wahart77399/RV-Bridge/src/Devices/Controllable/HVAC/FloorHeatView.cpp

#include "RVConstants.h"
#include "FloorHeatView.h"
#include "FloorHeat.h"
#include "Packet.h"
#include "DGN.h"
#include "debug.h"

float_t FloorHeatView::levelToTemperature(FLOOR_HEAT_LEVEL lvl) {
            return levelToTemperatureMap[lvl];
} 


boolean FloorHeatView::FloorHeatController::update(void) {
    boolean updated = false;
    if (/* (onOff != nullptr) && */ (targetTemp != nullptr) /* && (currentTemp != nullptr) */ && (model != nullptr) && (view != nullptr)) {
        view->dontUpdateTheView();
        if (/* onOff->updated()) { //  || */ targetTemp->updated() || targetState->updated()) {
            float_t closestTemp = view->closestTemperature(targetTemp->getNewVal<float_t>());
            //RV_PRINTF("FloorHeatView::FloorHeatController::update  - onOff: %d, targetTemp - %f\n", 
            //   onOff->getNewVal(), closestTemp);
            if (/* onOff->getNewVal() == false) { // || */ (targetState->getNewVal() == FLOOR_HEAT_OFF) || (closestTemp < FLOOR_HEAT_TEMP_STORE)) {
                model->turnFloorHeatOff();
                turnOff();
            } else {
                model->turnFloorHeatOn(closestTemp);
                turnOn();
                setTemperature(closestTemp);
            }
            updated = true;
        } 
        view->updateTheView();
    }
    return (updated);  
}


FloorHeatView::FloorHeatView(GenericDevice* model, const char* spanDevName) 
        : SpanView(model), controller(nullptr) {
}


bool FloorHeatView::updateView(void) {
    // RV_PRINTF("FloorHeatView::updateView called\n");
    bool updated = false;
    if (isNeedToUpdateView()) { // don't mess with the state of the lock when the change is is initiated by the controller and not the model
        uint8_t instance = indexOfModel();   
        uint8_t index = -1;
        FloorHeat* mdl = (FloorHeat* )getModel();
        if ((mdl != nullptr) && (controller != nullptr)) { 
            // RV_PRINTF("FloorHeatView::updateView - on = %d, & temp is %f\n", mdl->isTurnedOn(), mdl->currentFloorHeatSetting());
            if ((mdl->currentFloorHeatSetting() >= FLOOR_HEAT_TEMP_STORE) || mdl->isTurnedOn()) {
                //RV_PRINTF("FloorHeatView::updateView - on with temp = %f\n", mdl->currentFloorHeatSetting());
                controller->turnOn();
                controller->setTemperature(mdl->currentFloorHeatSetting() >= FLOOR_HEAT_TEMP_STORE ? 
                                            mdl->currentFloorHeatSetting() : FLOOR_HEAT_TEMP_STORE);

            } else {
                //RV_PRINTF("FloorHeatView::updateView - off\n");
                controller->turnOff();
            }
            updated = true;
        }        
    }

    // RV_PRINTF("FloorHeatView::updateView completed \n"); 
    return updated;
}

void FloorHeatView::createFloorHeatView(GenericDevice* model, const char* spanDevName) {
    RV_PRINTF("FloorHeatView::createAwningView called\n");

    FloorHeatView* vw = new FloorHeatView(model, spanDevName);

    SpanView::createAccessory();
    new Service::AccessoryInformation(); 
    new Characteristic::Identify();
    new Characteristic::Name(spanDevName);
    FloorHeatView::FloorHeatController* ctrl = new FloorHeatView::FloorHeatController(vw, (FloorHeat* )model);
    vw->setController(ctrl);

    if (vw != nullptr)
        RV_PRINTF("FloorHeatView::createAwningView: tmp created successfully\n");
    else
        RV_PRINTF("FloorHeatView::createAwningView: tmp creation failed\n");   
    RV_PRINTF("FloorHeatView::createAwningView completed\n");
}
