wahart77399/RV-Bridge/src/Devices/Controllable/HVAC/Thermostat.h

#ifndef THERMOSTAT_H
#define THERMOSTAT_H // once I'm ready to define this, move this below ifndef
/*********************************************************************************
 *  MIT License
 *  
 *  Copyright (c) 2023 Randy Ubillos
 *  
 *  https://github.com/rubillos/RV-Bridge
 *  
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
 ********************************************************************************/
 
////////////////////////////////////////////////////////////////
//                                                            //
//    RV-Bridge: A HomeKit to RV-C interface for the ESP32    //
//                                                            //
////////////////////////////////////////////////////////////////

//#define CUSTOM_CHAR_HEADER
#include "Arduino.h"
#include "GenericDevice.h"
#include "DGN.h"
#include "Packet.h"

#include "HVAC_defintions.h"
#include "RVConstants.h"
#include "debug.h"

// constexpr double  tempCOffset = -273.0;
// constexpr double  tempCScale = 0.03125;
// constexpr double  tempCRoundingOffset = -0.25;

class HVAC_Thermostat : public GenericDevice {

    private:
        // for THERMOSTAT_STATUS_1 which will be our base data
        const uint8_t THERMOSTAT_INDEX = 0;
        const uint8_t THERMOSTAT_OPERATING_MODE = 1;
        const uint8_t THERMOSTAT_FAN_SPEED = 2;
        const uint8_t THERMOSTAT_HEAT_TEMP_MSB = 3;
        const uint8_t THERMOSTAT_HEAT_TEMP_LSB = 4;
        const uint8_t THERMOSTAT_COOL_TEMP_MSB = 5;
        const uint8_t THERMOSTAT_COOL_TEMP_LSB = 6;
        const uint8_t OPERATING_MODE_MASK = 0x0f;
        const uint8_t FAN_MODE_MASK = 0x30;
        const uint8_t SCHEDULE_MODE_MASK = 0xc0;
        const uint8_t MAX_TEMP = 100;

        const uint8_t HEAT_TEMP_INDEX = 0;
        const uint8_t COLD_TEMP_INDEX = 1;
        uint16_t ambientTemperatureRaw_ = BAD_UINT16_DATA;
        bool ambientTemperatureAvailable_ = false;
        bool furnaceStatusAvailable_ = false;
        bool furnaceHeating_ = false;
        uint8_t airConditionerMode_ = 0xFF;
        uint8_t airConditionerMaxFanRaw_ = 0xFF;
        uint8_t heatPumpMode_ = 0xFF;
        uint8_t heatPumpMaxOutputRaw_ = 0xFF;
    public:
        /*
        static inline double convToTempC(uint16_t value) {
	        return tempCOffset + value * tempCScale + tempCRoundingOffset;  
        }
        static inline uint16_t convFromTempC(double tempC) {
	        return (tempC - tempCOffset + 0.5) / tempCScale;
        }
        */

    private:
        friend class ThermostatView;

        bool hasAmbientTemperature() const { return ambientTemperatureAvailable_; }
        double getAmbientTemperatureC() const {
            return ambientTemperatureAvailable_ ? convToTempC(ambientTemperatureRaw_) : INVALID_TEMPERATURE;
        }
        bool hasFurnaceStatus() const { return furnaceStatusAvailable_; }
        bool isFurnaceHeating() const { return furnaceHeating_; }
        void setAirConditionerStatus(const uint8_t* data) {
            if (data != nullptr) {
                airConditionerMode_ = data[1];
                airConditionerMaxFanRaw_ = data[2];
            }
        }
        void setHeatPumpStatus(const uint8_t* data) {
            if (data != nullptr) {
                heatPumpMode_ = data[1];
                heatPumpMaxOutputRaw_ = data[2];
            }
        }
        bool hasAirConditionerMode() const { return airConditionerMode_ <= 1; }
        uint8_t airConditionerMode() const { return airConditionerMode_; }
        bool hasAirConditionerMaxFan() const { return airConditionerMaxFanRaw_ <= MAX_RVC_PERCENT; }
        float airConditionerMaxFanPercent() const { return airConditionerMaxFanRaw_ * 0.5f; }
        bool hasHeatPumpMode() const { return heatPumpMode_ <= 1; }
        uint8_t heatPumpMode() const { return heatPumpMode_; }
        bool hasHeatPumpMaxOutput() const { return heatPumpMaxOutputRaw_ <= MAX_RVC_PERCENT; }
        float heatPumpMaxOutputPercent() const { return heatPumpMaxOutputRaw_ * 0.5f; }
        void setAmbientTemperature(const uint8_t* data) {
            if (data != nullptr) {
                ambientTemperatureRaw_ = static_cast<uint16_t>(data[1]) |
                                         (static_cast<uint16_t>(data[2]) << 8);
                double temperatureC = convToTempC(ambientTemperatureRaw_);
                ambientTemperatureAvailable_ = ambientTemperatureRaw_ != BAD_UINT16_DATA &&
                                               temperatureC >= -50.0 && temperatureC <= 100.0;
            }
        }
        void setFurnaceStatus(const uint8_t* data) {
            if (data != nullptr) {
                furnaceStatusAvailable_ = data[3] <= RVCPercentMax;
                furnaceHeating_ = furnaceStatusAvailable_ && data[3] > 0;
            }
        }

        void setFanMode(const RVCFanMode setting) {
            uint8_t* rawData = getCurrentData();
            if (rawData != nullptr) {
                uint8_t mode = rawData[THERMOSTAT_OPERATING_MODE];
                uint8_t mask = SCHEDULE_MODE_MASK | OPERATING_MODE_MASK;
                rawData[THERMOSTAT_OPERATING_MODE] = (mode & mask) | setting;
            }
        }
        void setOperatingMode(const RVCMode md) {
            uint8_t* rawData = getCurrentData();
            if (rawData != nullptr) {
                uint8_t mode = rawData[THERMOSTAT_OPERATING_MODE];
                uint8_t mask = SCHEDULE_MODE_MASK | FAN_MODE_MASK;
                rawData[THERMOSTAT_OPERATING_MODE] = (mode & mask) | md;
            }
        }

        void setFanSpeed(const RVCForcedFan speed) {
            uint8_t* rawData = getCurrentData();
            if (rawData != nullptr) {
                rawData[THERMOSTAT_FAN_SPEED] = speed;
            }
        }

        void setCoolTemp(const uint16_t tempC) {
            uint8_t* tempData = getCurrentData();
            if (tempData != nullptr) {
                uint16_t temp = convFromTempC(tempC);
                tempData[THERMOSTAT_COOL_TEMP_LSB] = temp >> 8;
                tempData[THERMOSTAT_COOL_TEMP_MSB] = temp & 0xff;
                RV_PRINTF("HVAC_Thermostat::setCoolTemp end - temp = tempData[5] %d, tempData[6] %d, Temp = %d", tempData[5], tempData[6], tempC);
            }
        }

        // all temps coming from °C to °C (storing in °C)
        void setHeatTemp(const uint16_t tempC) {
            uint8_t* tempData = getCurrentData();
            if (tempData != nullptr) {
                uint16_t temp = convFromTempC(tempC);
                tempData[THERMOSTAT_HEAT_TEMP_LSB] = temp >> 8;
                tempData[THERMOSTAT_HEAT_TEMP_MSB] = temp & 0xff;
            }
        }

        const RVCFanMode getFanMode(void) const {
            RVCFanMode modeResult = AUTO_FAN_MODE;
            uint8_t* rawData = getCurrentData();
            if (rawData != nullptr) {
                modeResult = (RVCFanMode) (rawData[THERMOSTAT_OPERATING_MODE] & FAN_MODE_MASK);
            }
            return modeResult;
        }

        const RVCForcedFan getFanSpeed(void) const {
            RVCForcedFan speed = AUTO_FAN;
            uint8_t* rawData = getCurrentData();
            if (rawData != nullptr) {
                speed = (RVCForcedFan) (rawData[THERMOSTAT_FAN_SPEED]);
            }
            return speed;
        }

        const RVCMode getOperatingMode(void) const {
            RVCMode modeResult = AUTO;
            uint8_t* rawData = getCurrentData();
            if (rawData != nullptr) {
                modeResult = (RVCMode) (rawData[THERMOSTAT_OPERATING_MODE] & OPERATING_MODE_MASK);
            }
            return modeResult;
        }

        const uint16_t getCoolTemp(void) const {
            uint16_t temp = DEFAULT_TEMP;
            uint8_t* tempData = getCurrentData();
            if (tempData != nullptr) {
                uint16_t tmp = convToTempC(tempData[THERMOSTAT_COOL_TEMP_LSB]<<8 | tempData[THERMOSTAT_COOL_TEMP_MSB]); 
                temp = (tmp < MAX_TEMP) ? tmp : DEFAULT_TEMP; //convFromTempC((double) tempC);

            }
            return temp;
        }

        const uint16_t getHeatTemp(void) const {
            uint16_t temp = DEFAULT_TEMP;
            uint8_t* tempData = getCurrentData();
            if (tempData != nullptr) {
                uint16_t tmp = convToTempC(tempData[THERMOSTAT_HEAT_TEMP_LSB]<<8 | tempData[THERMOSTAT_HEAT_TEMP_MSB]); 
                temp = (tmp < MAX_TEMP) ? tmp : DEFAULT_TEMP; //convFromTempC((double) tempC);
            }
            return temp;
        }

        boolean isFanAuto(void) const { return getFanMode() == AUTO_FAN_MODE; }

    protected:
        inline uint8_t* getCurrentData(void) const {
            return GenericDevice::getCurrentData();
        }
        
        virtual void setData(RVC_DGN dgn, uint8_t* data) {
            if (data != nullptr) {
                uint8_t* rawData = getCurrentData();
                uint8_t i = 1;
                if (rawData != nullptr) {// set the current data to the new data
                    switch (dgn) {
                        // COMMAND_1 and STATUS_1 have the same data format
                        case (THERMOSTAT_COMMAND_1):
                        case (THERMOSTAT_STATUS_1):
                            for (i = 1; i < 8; i++) // 8 bytes in a data payload
                                if (((i == 3) || (i == 4) || (i == 5) || (i==6)) && (data[i] == 0xff)) { // deals with out of bounds data
                                    rawData[i] = 0x24;
                                } else {
                                    rawData[i] = data[i];
                                }
                            break;
                    
                        default:
                            RV_PRINTF("********** WARNING: THESE THERMOSTAT DGNs ARE NOT SUPPORTED************* \n");
                            break;
                    }
                }
            }
        }

        virtual CAN_frame_t* buildCommand(RVC_DGN dgn);

    public:
        HVAC_Thermostat() : GenericDevice() { 
            // Constructor implementation
            
        }

        HVAC_Thermostat(const HVAC_Thermostat&) = delete;
        HVAC_Thermostat& operator=(const HVAC_Thermostat&) = delete;
        HVAC_Thermostat(HVAC_Thermostat&&) = delete;
        HVAC_Thermostat& operator=(HVAC_Thermostat&&) = delete;

        HVAC_Thermostat(uint8_t address, uint8_t instance) : GenericDevice(address, instance) {     
            
        }

        HVAC_Thermostat(uint8_t* data) : GenericDevice(data) {
            // Constructor with parameters implementation
        }

        virtual ~HVAC_Thermostat() {
            // Destructor implementation
        } 

        virtual boolean executeCommand(RVC_DGN dgn, const uint8_t* buffer, uint8_t val=SOURCE_ADDRESS);
};

#endif
