wahart77399/RV-Bridge/src/Devices/Controllable/HVAC/ThermostatView.cpp

/*********************************************************************************
 *  MIT License
 *  
 *  Copyright (c) 2023 Randy Ubillos
 *  
 *  https://github.com/rubillos/RV-Bridge
 *  
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
 ********************************************************************************/
 
////////////////////////////////////////////////////////////////
//                                                            //
//    RV-Bridge: A HomeKit to RV-C interface for the ESP32    //
//                                                            //
////////////////////////////////////////////////////////////////
#include "RVConstants.h"

#include "ThermostatView.h"
#include "Thermostat.h"
#include "Packet.h"
#include "DGN.h"
#include "debug.h"
 
bool ThermostatView::categoryCreated = false;
void ThermostatView::createCategory(void) {
    if (!categoryCreated) {
         categoryCreated = true;
    }
}
boolean ThermostatView::FanController::update(void) {
	bool updated = false;
    if ((_active != nullptr) && (speed != nullptr) && (targetState != nullptr) && (model != nullptr) && (view != nullptr)) {
        view->dontUpdateTheView();
	    if (_active->updated() || speed->updated() || targetState->updated()) {
		    RV_PRINTF("ThermostatView::FanController::update  - active: %d, speed - %d, targetState - %d\n", 
            _active->getNewVal(), speed->getNewVal(), targetState->getNewVal());
            // updated = view->updateView();
            if (speed->updated()) {
                float spd = speed->getNewVal();
                float lowSpeed = view->HomeKitPercentMax/2;
                RVCForcedFan newSpeed = AUTO_FAN;
                if (spd > 0)
                    newSpeed = (spd <= lowSpeed) ? LOW_FAN : HIGH_FAN;
                model->setFanSpeed(newSpeed);
            }
            if (_active->updated() && (_active->getNewVal() > 0)) 
                model->setFanMode(ON_FAN_MODE);
            else  
                model->setFanMode(AUTO_FAN_MODE);
            model->executeCommand(THERMOSTAT_COMMAND_1, model->getCurrentData());
        }
        view->updateTheView();
    }
	return (updated);  
}

RVCFanMode ThermostatView::FanController::getMode(void) const {
    RVCFanMode mode = AUTO_FAN_MODE;
    if ((_active != nullptr) && (_active->getVal() > 0))
        mode = ON_FAN_MODE;
    return mode;
}

uint16_t ThermostatView::FanController::getSpeed(void) const {
    uint16_t speedResult = (uint16_t) AUTO_FAN;
    if (speed != nullptr) {
        float spd = speed->getVal();
        float lowSpeed = view->HomeKitPercentMax/2;
        if (spd > 0)
            speedResult = (spd <= lowSpeed) ? (uint16_t) LOW_FAN : (uint16_t) HIGH_FAN;
    }
    return speedResult;
}

#include "PacketQueue.h"

 void ThermostatView::FanController::setModeSpeed(uint8_t fanMode, uint8_t spd) {
	bool newActive = fanMode == ON_FAN_MODE;

    if (view != nullptr) {
    	spd = spd * view->HomeKitPercentMax / RVCPercentMax;

	    if ((_active != nullptr) && (newActive != _active->getVal())) {
		    RV_PRINTF("Thermostat::FanController::setModeSpeed #%d - setActive: %d\n", (uint32_t)millis(), model->index(), newActive);
		    _active->setVal(newActive);
	    }
	    if ((speed != nullptr) && (spd != speed->getVal())) {
		    RV_PRINTF("Thermostat::FanController::setModeSpeed #%d - setSpeed: %d\n", model->index(), spd);
		    speed->setVal((spd < 100) ? spd : INITIAL_ROTATION_SPEED);
        }
        PacketQueue::clearLastPacketReceiveTime();
    }
} 



void ThermostatView::FanController::setLevel(uint8_t level) {
	bool on = level > 0;
	bool changed = false;

    if ((model != nullptr) && (!model->isFanAuto())) {
        if ((level > 0) && (level <= view->HomeKitPercentMax)) {
            currentState->setVal(currentFanStateBlowing);
        } else {
            currentState->setVal(currentFanStateIdle);
        }
        PacketQueue::clearLastPacketReceiveTime();
    }
} 
    //*/


typedef enum {
    THERM_OFF=0,
    THERM_HEAT = 1,
    THERM_COOL = 2,
    THERM_AUTO = 3
} HomeKitOperatingMode;

boolean ThermostatView::ThermostatController::update(void) {
    boolean updated = false;
    if ((targetState != nullptr) && (targetTemp != nullptr) && (model != nullptr) && (view != nullptr)) {
        view->dontUpdateTheView();
        HVAC_Thermostat* myModel = model;
        if (targetState->updated()) {
            switch(targetState->getNewVal()) {
                case (THERM_OFF):
                    myModel->setOperatingMode(RVCMode::OFF);
                    break;
                case (THERM_HEAT):
                    myModel->setOperatingMode(RVCMode::HEAT);
                    break;
                case(THERM_COOL):
                    myModel->setOperatingMode(RVCMode::COOL);
                    break;
                case(THERM_AUTO):
                default:
                    myModel->setOperatingMode(RVCMode::AUTO);
                    break;
            }
            updated = true;
        }
        if (targetTemp->updated()) {
            RVCMode md = myModel->getOperatingMode();
            float temp = targetTemp->getNewVal();
            switch (md) {
                case (RVCMode::COOL):
                    myModel->setCoolTemp(temp);
                    break;
                case(RVCMode::HEAT):
                    myModel->setHeatTemp(temp);
                    break;
                case (RVCMode::AUTO):
                    myModel->setCoolTemp(temp);
                    myModel->setHeatTemp((temp - 4.0));
                    break;
                case(RVCMode::OFF):
                default:
                    // do nothing
                    break;
            }
        }
        myModel->executeCommand(THERMOSTAT_COMMAND_1, myModel->getCurrentData());
        updated = true;
        view->updateTheView();
    }
    return updated;
}

void ThermostatView::ThermostatController::setInfo(RVCMode opMode, RVCFanMode fanMode, RVCForcedFan fanSpeed,
                                                   double heatTemp, double coolTemp, bool hasAmbientTemp,
                                                   double ambientTempC, bool hasFurnaceStatus,
                                                   bool furnaceHeating) {
    if ((currentState != nullptr) && (targetState != nullptr) && (targetTemp != nullptr) && (fan != nullptr) && (ambientTemp != nullptr)) {
        if (hasAmbientTemp && fabs(ambientTemp->getVal<double>() - ambientTempC) > 0.05) {
            ambientTemp->setVal(ambientTempC);
        }
        HomeKitOperatingMode homeKitOperatingMode = static_cast<HomeKitOperatingMode>(targetState->getVal<uint8_t>());
        switch(opMode) {
            case (RVCMode::COOL):
                
                switch (homeKitOperatingMode) {
                    case(THERM_OFF):
                    case(THERM_AUTO):
                    case(THERM_HEAT):
                        targetState->setVal(THERM_COOL);
                        break;
                    case(THERM_COOL):
                    default:
                        break;
                        // do nothing
                }
                if (fabs(coolTemp - targetTemp->getVal<double>()) > 0.2) {
	    			    // RV_PRINTF("ThermostatView::ThermostatController - Cool Thermostat #%d: targetTemp = %f\n", model->index(), coolTemp);
		    		    targetTemp->setVal(coolTemp);
		        }
                
                break;
            case (RVCMode::HEAT):
                switch(homeKitOperatingMode) {
                    case(THERM_OFF):
                    case(THERM_AUTO):
                    case(THERM_COOL):
                        targetState->setVal(THERM_HEAT);
                        break;
                    case(THERM_HEAT):
                    default:
                        break;
                        // do nothing
                }
                if (fabs(heatTemp - targetTemp->getVal<double>()) > 0.2) {
	    			    // RV_PRINTF("ThermostatView::ThermostatController - Heat Thermostat #%d: targetTemp = %f\n", model->index(), heatTemp);
		    		    targetTemp->setVal(heatTemp);
		        }
                break;
            case (RVCMode::AUTO):
                switch(homeKitOperatingMode) {
                    case(THERM_OFF):
                    case(THERM_COOL):
                    case(THERM_HEAT):
                        targetState->setVal(THERM_AUTO);
                        break;
                    case (THERM_AUTO):
                    default:
                        // do nothing
                        break;
                }
                if (ambientTemp->getVal() > coolTemp) 
                    targetTemp->setVal(coolTemp);
                else if (ambientTemp->getVal() < heatTemp)
                    targetTemp->setVal(heatTemp);
                break;
            case (RVCMode::OFF):
                switch(homeKitOperatingMode) {
                    case(THERM_COOL):
                    case(THERM_HEAT):
                    case(THERM_AUTO):
                        targetState->setVal(THERM_OFF);
                        break;
                    case(THERM_OFF):
                    default:
                        // do nothing
                        break;
                }
                break;
            default:
                break;
        }
        if (hasFurnaceStatus) {
            uint8_t heatingState = furnaceHeating
                ? HomeKitHVACStates::heatingCoolingStateHeat
                : HomeKitHVACStates::heatingCoolingStateOff;
            if (currentState->getVal<uint8_t>() != heatingState) currentState->setVal(heatingState);
        }
        fan->setModeSpeed(fanMode, fanSpeed);
        PacketQueue::clearLastPacketReceiveTime();
    }
}

#include "ChassisMobility.h"

bool ThermostatView::updateView(void) {
        // 
    // RV_PRINTF("DoorLockView::updateView called\n");
    bool updated = false;
    if (isNeedToUpdateView() && ChassisMobility::isParked()) { // don't mess with the state of the lock when the change is is initiated by the controller and not the model
        uint8_t instance = indexOfModel();   
        uint8_t index = -1;
        HVAC_Thermostat* mdl = (HVAC_Thermostat* )getModel();
        if ((mdl != nullptr) && (controller != nullptr)) {
            RVCFanMode fanMode = mdl->getFanMode();
            RVCMode opMode = mdl->getOperatingMode();
            RVCForcedFan fanSpeed = mdl->getFanSpeed();
            float coolTemp = mdl->getCoolTemp();
            float heatTemp = mdl->getHeatTemp();
            controller->setInfo(opMode, fanMode, fanSpeed, heatTemp, coolTemp,
                                mdl->hasAmbientTemperature(), mdl->getAmbientTemperatureC(),
                                mdl->hasFurnaceStatus(), mdl->isFurnaceHeating());
            if (mdl->hasAirConditionerMode() && airConditionerModeChar_ != nullptr) {
                airConditionerModeChar_->setVal(tempCfromTempF(mdl->airConditionerMode()));
            }
            if (mdl->hasAirConditionerMaxFan() && airConditionerMaxFanChar_ != nullptr) {
                airConditionerMaxFanChar_->setVal(tempCfromTempF(mdl->airConditionerMaxFanPercent()));
            }
            if (mdl->hasHeatPumpMode() && heatPumpModeChar_ != nullptr) {
                heatPumpModeChar_->setVal(tempCfromTempF(mdl->heatPumpMode()));
            }
            if (mdl->hasHeatPumpMaxOutput() && heatPumpMaxOutputChar_ != nullptr) {
                heatPumpMaxOutputChar_->setVal(tempCfromTempF(mdl->heatPumpMaxOutputPercent()));
            }
            updated = true; 
        }
    }
    // RV_PRINTF("DoorLockView::updateView completed \n"); 
    return updated;
 }

 ThermostatView::ThermostatView(GenericDevice* model, const char* spanDevName)
     : SpanView(model)
     , controller(nullptr)
     , airConditionerModeChar_(nullptr)
     , airConditionerMaxFanChar_(nullptr)
     , heatPumpModeChar_(nullptr)
     , heatPumpMaxOutputChar_(nullptr) {

 }

 void ThermostatView::createThermostatView(GenericDevice* model, const char* spanDevName) {
    RV_PRINTF("ThermostatView::createThermostatView called\n");
    SpanView::prepHomeSpan();

    ThermostatView* vw = new ThermostatView(model, spanDevName);

    ThermostatView::createCategory();

    const String fanName = String(spanDevName) + " Fan";
    SpanView::createAccessory();
    new Service::AccessoryInformation(); 
    new Characteristic::Identify();
    new Characteristic::Name(fanName.c_str());
    ThermostatView::FanController* fn = new ThermostatView::FanController(vw, (HVAC_Thermostat*)model);

    SpanView::createAccessory();
    new Service::AccessoryInformation(); 
    new Characteristic::Identify();
    new Characteristic::Name(spanDevName);

    ThermostatView::ThermostatController* controller = new ThermostatView::ThermostatController(vw, model, fn, spanDevName);
    vw->setController(controller);

    new Service::TemperatureSensor();
        new Characteristic::ConfiguredName("A/C Mode (0 Auto, 1 Manual)");
    vw->airConditionerModeChar_ = new Characteristic::CurrentTemperature(tempCfromTempF(0));
    vw->airConditionerModeChar_->setRange(tempCfromTempF(0), tempCfromTempF(1));

    new Service::TemperatureSensor();
        new Characteristic::ConfiguredName("A/C Max Fan Speed (%)");
    vw->airConditionerMaxFanChar_ = new Characteristic::CurrentTemperature(tempCfromTempF(0));
    vw->airConditionerMaxFanChar_->setRange(tempCfromTempF(0), tempCfromTempF(MAX_RVC_PERCENT * RVC_PERCENT_PRECISION));

    new Service::TemperatureSensor();
        new Characteristic::ConfiguredName("Heat Pump Mode (0 Auto, 1 Manual)");
    vw->heatPumpModeChar_ = new Characteristic::CurrentTemperature(tempCfromTempF(0));
    vw->heatPumpModeChar_->setRange(tempCfromTempF(0), tempCfromTempF(1));

    new Service::TemperatureSensor();
        new Characteristic::ConfiguredName("Heat Pump Max Output (%)");
    vw->heatPumpMaxOutputChar_ = new Characteristic::CurrentTemperature(tempCfromTempF(0));
    vw->heatPumpMaxOutputChar_->setRange(tempCfromTempF(0), tempCfromTempF(MAX_RVC_PERCENT * RVC_PERCENT_PRECISION));


    if (vw != nullptr)
        RV_PRINTF("ThermostatView::createThermostatView: tmp created successfully\n");
    else
        RV_PRINTF("ThermostatView::createThermostatView: tmp creation failed\n");   
    RV_PRINTF("ThermostatView::createThermostatView completed\n");
}
