wahart77399/RV-Bridge/src/Devices/Sensors/Power/Battery.h

#include "RVConstants.h"
#include "debug.h"
#ifndef BATTERY_H
#define BATTERY_H // once I'm ready to define this, move this below ifndef

/*********************************************************************************
 *  MIT License
 *  
 *  Copyright (c) 2023 Randy Ubillos
 *  
 *  https://github.com/rubillos/RV-Bridge
 *  
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
 ********************************************************************************/
 
////////////////////////////////////////////////////////////////
//                                                            //
//    RV-Bridge: A HomeKit to RV-C interface for the ESP32    //
//                                                            //
////////////////////////////////////////////////////////////////

//#define CUSTOM_CHAR_HEADER
#include "Arduino.h"
#include "GenericDevice.h"
#include "RVConstants.h"
#include "BatteryDefinitions.h"
#include "byteswap.h"
#include <limits>

class Battery : public GenericDevice {
    private:
         
        uint8_t* source2Data;
        uint8_t* source3Data;
        uint8_t* source4Data;
        bool dcDisconnectStatusAvailable_ = false;
        bool dcConnected_ = false;

        const uint8_t TIME_TO_EMPTY = 0x00;
        const uint8_t TIME_TO_FULL = 0x01;
        friend class BatteryView;
        uint8_t* getSource1Data(void) const { return getCurrentData();} 
        uint8_t* getSource2Data(void) const { return source2Data; }
        uint8_t* getSource3Data(void) const { return source3Data; }
        uint8_t* getSource4Data(void) const { return source4Data; }

        static inline uint32_t rd_le32(const uint8_t* p) {
            return (uint32_t)p[0] | ((uint32_t)p[1] << 8) | ((uint32_t)p[2] << 16) | ((uint32_t)p[3] << 24);
        }

        void setDataFromSource(uint8_t* source, uint8_t* destination) {
            if ((source != nullptr) && (destination != nullptr)) {
                for (int i = DC_SOURCE_PRIORITY_INDEX; i < (DC_SOURCE_CURRENT_LSB_2_INDEX + 1); i++)
                    destination[i] = source[i];
            }
        }

        const DC_SOURCE_INSTANCE_DEFINITION getSourceDefinition(void) const {
            DC_SOURCE_INSTANCE_DEFINITION result = INVALID_SOURCE;
            uint8_t* data = getCurrentData();
            if (data != nullptr)
                result = (DC_SOURCE_INSTANCE_DEFINITION) data[DC_SOURCE_INSTANCE_INDEX];
            return result;
        }

        const DC_SOURCE_PRIORITY_DEFINTION getPirorityDefinition(void) const {
            DC_SOURCE_PRIORITY_DEFINTION result = NO_PRIORITY_ALWAYS_RPT;
            uint8_t* data = getCurrentData();
            if (data != nullptr)
                result = (DC_SOURCE_PRIORITY_DEFINTION) data[DC_SOURCE_PRIORITY_INDEX];
            return result;
        }

        // SOURCE 1 STATUS Data
        float_t directCurrentVoltage(void) const {
            uint8_t* data = getSource1Data();
            uint16_t value = 0;
            float_t result = std::numeric_limits<float_t>::quiet_NaN();
            if (data != nullptr) {
                value = getLilEndian(data[DC_SOURCE_VOLTAGE_MSB_INDEX], data[DC_SOURCE_VOLTAGE_LSB_INDEX]);
                if (value <= VDC_RAW_MAX)
                    result = (value - VDC_OFFSET) * VDC_PRECISION;
            }
            return result;
        }

        float directCurrentAmperage(void) const {
            uint8_t* data = getSource1Data();
            float result = std::numeric_limits<float>::quiet_NaN();
            if (data != nullptr) {
                const uint8_t* cur = &data[DC_SOURCE_CURRENT_MSB_1_INDEX];
                uint32_t raw = rd_le32(cur);
                if (raw != 0xFFFFFFFFu) {
                    result = (static_cast<float>(static_cast<int64_t>(raw) - static_cast<int64_t>(ADC_ZERO))) 
                              * static_cast<float>(ADC_PRECISION);
                }
            }
            return result;
        }

        // SOURCE 2 STATUS DATA
        const double temperature(void) const {
            uint8_t* data = getSource2Data();
            double result = INVALID_TEMPERATURE;
            if (data != nullptr) {
                uint16_t rawTemperature = getLilEndian(data[DC_SOURCE_TEMPERATURE_MSB_INDEX], data[DC_SOURCE_TEMPERATURE_LSB_INDEX]);
                if (rawTemperature != BAD_UINT16_DATA) {
                    result = convToTempC(rawTemperature);
                }
                // RV_PRINTF("Battery::temperature = %d\n", result);
            }
            return result;
        }

        uint8_t level(void) const {
            uint8_t* data = getSource2Data();
            uint8_t result = OUT_OF_RANGE_DATA;
            if ((data != nullptr) && (data[DC_SOURCE_STATE_OF_CHARGE_INDEX] <= MAX_RVC_PERCENT)) {
                uint8_t tmp = data[DC_SOURCE_STATE_OF_CHARGE_INDEX];
                RV_PRINTF("Battery::level tmp = %d\n", tmp);
                result = static_cast<uint8_t>(static_cast<float_t>(tmp) * RVC_PERCENT_PRECISION);
                // RV_PRINTF("Battery::level result = %d\n", result);
            }
            return result;
        }
        /* REMOVED - not currently used by Newmar
        const uint16_t timeRemaining(void) const {
            uint8_t* data = getSource2Data();
            uint16_t result = OUT_OF_RANGE_DATA;
            if (data != nullptr) {
                uint8_t tmp = getLilEndian(data[DC_SOURCE_TIME_REMAINING_MSB_INDEX], data[DC_SOURCE_TIME_REMAINING_LSB_INDEX]);
                if (tmp != 0xffff) {
                    result = tmp;
                    RV_PRINTF("Battery::timeRemaining = %d\n", result);
                }
            } else {
                RV_PRINTF("Battery::timeRemaining data is not valid\n");
            }
            return result;
        }
        
        const boolean timeToEmpty(void) const {
            boolean empty = true;
            uint8_t* data = getSource2Data();
            if (data != nullptr) {
                empty = data[DC_SOURCE_TIME_INTERPRETATION] == TIME_TO_EMPTY;
                // RV_PRINTF("Battery::timeToEmpty = %d\n", empty);
            }
            return empty;
        } 
        */

        // SOURCE 3 STATUS DATA
        /* REMOVED - not currently used by Newmar
        const uint8_t health(void) const {
            uint8_t* data = getSource3Data();
            uint8_t result = OUT_OF_RANGE_DATA;
            if (data != nullptr) {
                result = data[DC_SOURCE_HEALTH_STATE_INDEX];
                RV_PRINTF("Battery::health = %d\n", result);
            } else {
                RV_PRINTF("Battery::health data is not valid\n");
            }
            return result;
        }
        

        const uint16_t remainingCapacity(void) const {
            uint8_t* data = getSource3Data();
            uint16_t result = OUT_OF_RANGE_DATA;
            if (data != nullptr) {
                result = /* convFromTempC( * getLilEndian(data[DC_SOURCE_CAP_REMAINS_MSB_INDEX], data[DC_SOURCE_CAP_REMAINS_LSB_INDEX]); //);
                // RV_PRINTF("Battery::remaining capacity = %d\n", result);
                if (result == INVALID_AMP_HOURS)
                    result = OUT_OF_RANGE_DATA;
            } else {
                RV_PRINTF("Battery::remaining capacity data is not valid\n");
            }
            return result;
        }

        * REMOVED - not currently used by Newmar
        const uint8_t relativeCapacity(void) const {
            uint8_t* data = getSource3Data();
            uint8_t result = OUT_OF_RANGE_DATA;
            if (data != nullptr) {
                result = data[DC_SOURCE_RELATIVE_CAP_INDEX];
                RV_PRINTF("Battery:relativeCapacity percenatge = %d\n", result);
            } else {
                RV_PRINTF("Battery::relativeCapacity data is not valid\n");
            }
            return result;
        }
        */
        uint16_t rmsRipple(void) const {
            uint8_t* data = getSource3Data();
            uint16_t result = INVALID_RMS_RIPPLE;
            if (data != nullptr) {
                result = /* convFromTempC */ (getLilEndian(data[DC_SOURCE_AC_RIPPLE_MSB_INDEX], data[DC_SOURCE_AC_RIPPLE_LSB_INDEX]));
                // RV_PRINTF("Battery::rmsRipple = %d\n", result);
                if (result > 65530)
                    result = INVALID_RMS_RIPPLE;
            }
            return result;
        }

        // SOURCE 4 STATUS DATA
        /* REMOVED - not currently used by Newmar
        const CHARGE_STATE chargeState(void) const {
            uint8_t* data = getSource4Data();
            CHARGE_STATE result = UNDEFINED_CHARGE_STATE;
            if (data != nullptr) {
                result = (CHARGE_STATE) data[DC_SOURCE_DESORED_CHARGE_STATE_INDEX];
                RV_PRINTF("Battery::chargeState = %d\n", result);
            } else {
                RV_PRINTF("Battery::chargeState data is not valid\n");
            }
            return result;
        }

        const uint16_t desiredVoltage(void) const {
            uint8_t* data = getSource4Data();
            uint16_t result = OUT_OF_RANGE_DATA;
            if (data != nullptr) {
                result = getLilEndian(data[DC_SOURCE_DESIRED_VOLT_MSB_INDEX], data[DC_SOURCE_DESIRED_VOLT_LSB_INDEX]);
                RV_PRINTF("Battery::desiredVoltage = %d\n", result);
            } else {
                RV_PRINTF("Battery::desiredVoltage data is not valid\n");
            }
            return result;
        }

        const uint16_t desiredCurrent(void) const {
            uint8_t* data = getSource4Data();
            uint16_t result = OUT_OF_RANGE_DATA;
            if (data != nullptr) {
                result = getLilEndian(data[DC_SOURCE_DESIRED_AMP_MSB_INDEX], data[DC_SOURCE_DESIRED_AMP_LSB_INDEX]);
                RV_PRINTF("Battery::desiredCurrent = %d\n", result);
            } else {
                RV_PRINTF("Battery::desiredCurrent data is not valid\n");
            }
            return result;
        }

        const BATTERY_TYPE type(void) const {
            uint8_t* data = getSource4Data();
            BATTERY_TYPE result = FLOODED_BATTERY;
            if (data != nullptr) {
                result = (BATTERY_TYPE) data[DC_SOURCE_BATTERY_TYPE_INDEX];
                RV_PRINTF("Battery::battery type = %d\n", result);
            } else {
                RV_PRINTF("Battery::battery type data is not valid\n");
            }
            return result;  
        }
        */

    protected:
        
        // virtual CAN_frame_t* buildCommand(RVC_DGN dgn); // do nothing - no commands will be sent to the ATS - we listen only
        virtual void setData(RVC_DGN dgn, uint8_t* data) {
            if (data != nullptr) {
                switch (dgn) {
                    case (DC_SOURCE_STATUS_1):
                        setDataFromSource(data, getSource1Data());
                        break;
                    case (DC_SOURCE_STATUS_2):
                        setDataFromSource(data, getSource2Data());
                        break;
                    case (DC_SOURCE_STATUS_3):
                        setDataFromSource(data, getSource3Data());
                        break;
                    case (DC_SOURCE_STATUS_4):
                        setDataFromSource(data, getSource4Data());
                        break;
                    case (DC_DISCONNECT_STATUS): {
                        uint8_t circuitStatus = data[1] & 0x03;
                        dcDisconnectStatusAvailable_ = circuitStatus <= 1;
                        if (dcDisconnectStatusAvailable_) {
                            dcConnected_ = circuitStatus == 1;
                        }
                        break;
                    }
                    default:
                        RV_PRINTF("Battery::setData failed = no matching dgn - dgn= %0x\n", dgn);
                }
            }
        }

        virtual CAN_frame_t* buildCommand(RVC_DGN dgn); // do nothing - no commands will be sent to the BATTERY - we listen only


    public:
        Battery() : GenericDevice(), source2Data(nullptr), source3Data(nullptr), source4Data(nullptr) {
            // Constructor implementation
        }


        Battery(const Battery&) = delete;
        Battery& operator=(const Battery&) = delete;


        Battery(uint8_t address, uint8_t index, uint8_t pri) : GenericDevice(address, index), source2Data(nullptr), source3Data(nullptr), source4Data(nullptr) { 
            uint8_t* data = getCurrentData();
            if (data != nullptr)
                data[DC_SOURCE_PRIORITY_INDEX] = pri;
            source2Data = new uint8_t[sizeof(uint8_t) * 8];
            source2Data[DC_SOURCE_INSTANCE_INDEX] = index;
            source2Data[DC_SOURCE_PRIORITY_INDEX] = pri;
            for (uint8_t i = 2; i < 8; i++) {
                source2Data[i] = OUT_OF_RANGE_DATA; // initialize to invalid data
            }
            source3Data = new uint8_t[sizeof(uint8_t) * 8];
            source3Data[DC_SOURCE_INSTANCE_INDEX] = index;
            source3Data[DC_SOURCE_PRIORITY_INDEX] = pri;
            for (uint8_t i = 2; i < 8; i++) {
                source3Data[i] = OUT_OF_RANGE_DATA; // initialize to invalid data
            }
            source4Data = new uint8_t[sizeof(uint8_t) * 8];
            source4Data[DC_SOURCE_INSTANCE_INDEX] = index;
            source4Data[DC_SOURCE_PRIORITY_INDEX] = pri;
            for (uint8_t i = 2; i < 8; i++) {
                source4Data[i] = OUT_OF_RANGE_DATA; // initialize to invalid data
            }
        }


        Battery(uint8_t* data) : GenericDevice(data), source2Data(nullptr), source3Data(nullptr), source4Data(nullptr) {
            // Constructor with parameters implementation
        }


        Battery(Battery&&) = delete;
        Battery& operator=(Battery&&) = delete;

        virtual ~Battery() {
            // Destructor implementation
            delete[] source2Data;
            delete[] source3Data;
            delete[] source4Data;
        } 


        virtual boolean executeCommand(RVC_DGN dgn, const uint8_t* buffer, uint8_t val=SOURCE_ADDRESS); // this is only to deal with Batetery dgns
};

#endif
