wahart77399/RV-Bridge/src/Devices/Controllable/Switches/LightDevice.cpp

/*********************************************************************************
 *  MIT License
 *  
 *  Copyright (c) 2023 Randy Ubillos
 *  
 *  https://github.com/rubillos/RV-Bridge
 *  
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
 ********************************************************************************/
 
////////////////////////////////////////////////////////////////
//                                                            //
//    RV-Bridge: A HomeKit to RV-C interface for the ESP32    //
//                                                            //
////////////////////////////////////////////////////////////////
#include "RVConstants.h"
#include "Arduino.h"
#include "LightDevice.h"
#include "Packet.h"
#include "debug.h"


CAN_frame_t* LightDevice::buildCommand(RVC_DGN dgn) {
    RV_PRINTF("LightDevice::buildCommand called with dgn=%#x\n", dgn);
    CAN_frame_t* frame = GenericDevice::buildCommand(dgn); // initiates the building of the frame => starting with instance and the dgn (ie the first 2 bytes)
    if (frame != nullptr) {
        RV_PRINTF("LightDevice::buildCommand: frame built with MsgID=%#x\n", frame->MsgID);
        const uint8_t* sendData = getCurrentData(); 
        const char* buff = nullptr;
        switch (dgn) {
            case DC_DIMMER_COMMAND: {                // Handle second DC Dimmer command
                RV_PRINTF("LightDevice::buildCommand: Handling DC_DIMMER_COMMAND\n");
                uint8_t* d = frame->data.u8;
                // int16_t i;
                // char* cval = (char* )sendData;
                // int16_t val = atoi(cval); // Convert the first character to an integer value
                // buff = Packet::parseBufferForValuePair(sendData, i, val); 
                //RV_PRINTF("LightDevice::buildCommand: val=%d\n", val);
                if ((d != nullptr) && (sendData != nullptr )) {
                    // Handle switch ON command for second dimmer
                    RV_PRINTF("On/Offf command received with %u value.\n", sendData[DC_DIMMER_COMMAND_BRIGHTNESS_INDEX]);
                    
                    d[DC_DIMMER_COMMAND_BRIGHTNESS_INDEX] = sendData[DC_DIMMER_COMMAND_BRIGHTNESS_INDEX]; // Full brightness value -> RVCBrightMax
                    d[2] = sendData[2]; // ff
	                d[3] = sendData[3]; // ff 
	                d[4] = sendData[4]; // ff
	                d[5] = sendData[5]; // ff

                    RV_PRINTF("LightDevice::buildCommand: d[0]=%d, d[1]=%d, d[2]=%d, d[3]=%d, d[4]=%d, d[5]=%d, d[6]=%d, d[7]=%d, getOnFlag=%d\n", 
                           d[0], d[1], d[2], d[3], d[4], d[5], d[6], d[7], isOn());

                } else {
                    // Handle unknown command for second dimmer
                    RV_PRINTF("Unknown command received.\n");
                }
                break;
            }
            case DC_DIMMER_STATUS_1:
                // Handle DC Dimmer Status 1
                RV_PRINTF("DC Dimmer Status 1 received.\n");
                // Process status data if needed
                break;

            case DC_DIMMER_STATUS_2:
                // Handle DC Dimmer Status 2
                RV_PRINTF("DC Dimmer Status 2 received.\n");
                // Process status data if needed 
                break;
            
            case DC_DIMMER_STATUS_3: // goes with DC_DIMMER_COMMAND_2
                // Handle DC Dimmer Status 3
                RV_PRINTF("DC Dimmer Status 3 received.\n");
                // Process status data if needed
                break;
            case DC_LIGHTING_CONTROLLER_STATUS_1:     
                // Handle DC Lighting Controller Status 1
                RV_PRINTF("DC Lighting Controller Status 1 received.\n");
                // Process status data if needed
                break;

            case DC_LIGHTING_CONTROLLER_STATUS_2:
                // Handle DC Lighting Controller Status 2
                RV_PRINTF("DC Lighting Controller Status 2 received.\n");
                // Process status data if needed
                break;
            case DC_LIGHTING_CONTROLLER_STATUS_3:
                // Handle DC Lighting Controller Status 3
                RV_PRINTF("DC Lighting Controller Status 3 received.\n");
                // Process status data if needed
                break;
            case DC_LIGHTING_CONTROLLER_STATUS_4:
                // Handle DC Lighting Controller Status 4
                RV_PRINTF("DC Lighting Controller Status 4 received.\n");
                // Process status data if needed
                break;
            case DC_LIGHTING_CONTROLLER_STATUS_5:
                // Handle DC Lighting Controller Status 5
                RV_PRINTF("DC Lighting Controller Status 5 received.\n");
                // Process status data if needed
                break;
            case DC_LIGHTING_CONTROLLER_STATUS_6:
                // Handle DC Lighting Controller Status 6
                RV_PRINTF("DC Lighting Controller Status 6 received.\n");
                // Process status data if needed
                break;
            case DC_LIGHTING_CONTROLLER_COMMAND_1:
                // Handle DC Lighting Controller Command 1
                RV_PRINTF("DC Lighting Controller Command 1 received.\n");
                // Process command data if needed
                break;
            case DC_LIGHTING_CONTROLLER_COMMAND_2:
                // Handle DC Lighting Controller Command 2
                RV_PRINTF("DC Lighting Controller Command 2 received.\n");
                // Process command data if needed
                break;
            case DC_LIGHTING_CONTROLLER_COMMAND_3:
                // Handle DC Lighting Controller Command 3
                RV_PRINTF("DC Lighting Controller Command 3 received.\n");
                // Process command data if needed
                break;
            case DC_LIGHTING_CONTROLLER_COMMAND_4:
                // Handle DC Lighting Controller Command 4
                RV_PRINTF("DC Lighting Controller Command 4 received.\n");
                // Process command data if needed
                break;
            case DC_LIGHTING_CONTROLLER_COMMAND_5:
                // Handle DC Lighting Controller Command 5
                RV_PRINTF("DC Lighting Controller Command 5 received.\n");
                // Process command data if needed
                break;
            case DC_LIGHTING_CONTROLLER_COMMAND_6: 
                // Handle DC Lighting Controller Command 6
                RV_PRINTF("DC Lighting Controller Command 6 received.\n");
                // Process command data if needed
            default:
                // Handle other commands or unknown DGN
                break;
        }
        
    }
    return frame;
}

/**
void LightDevice::printPacketData(RVC_DGN dgn, uint8_t* data, PacketPrint printPacket) {
    GenericDevice::printPacketData(dgn, data, printPacket);
    if (printPacket == packetPrintIfKnown || printPacket == packetPrintYes) {
        // Print additional information specific to DC Switch
    }
}
*/

#include "PacketQueue.h"

boolean LightDevice::executeCommand(RVC_DGN dgn, const uint8_t* data, uint8_t sAddress) {
    // RV_PRINTF("LightDevice::executeCommand called with dgn=%#x\n", dgn);
    boolean cmdExecuted = GenericDevice::executeCommand(dgn, data);
    if (!cmdExecuted) { // && (data != nullptr)) {
        // RV_PRINTF("LightDevice::executeCommand: Command not executed, building command for dgn=%#x\n", dgn);
        CAN_frame_t* frame = nullptr;
        uint8_t* rawData = (uint8_t* )data;
        switch (dgn) {
            case (DC_DIMMER_COMMAND): {
                if (sAddress == SOURCE_ADDRESS) {
                    // RV_PRINTF("LightDevice::executeCommand: Handling DC_DIMMER_COMMAND\n");
                    // need to send the command on the CAN BUS
                    frame = buildCommand(dgn);
                    if (frame != nullptr) {
                        // RV_PRINTF("LightDevice::executeCommand: Sending command on CAN bus with MsgID=%#x\n", frame->MsgID);
                        PacketQueue::queuePacket(*frame); //Packet::queueItUpForSend(frame);
                    }
                } else {
                    // a command was issued by another controller, not a homekit controller = need to reflect the change 
                    // in homekit, so update the views on the model
                    updateViews(); // it came from the CAN bus, so we update the views
                }
                cmdExecuted  = true;
                break;
            }
            case (DC_DIMMER_COMMAND_2):
                RV_PRINTF("LightDevice::executeCommand: Handling DC_DIMMER_COMMAND_2 not supported in 2022 ESSEX\n");
                break;
            case (DC_DIMMER_STATUS_1):
                RV_PRINTF("LightDevice::executeCommand: !!!!!!!!!! CURRENTLY DO NOT Handle DC_DIMMER_STATUS_1 or 2 !!!!!!!!!!!!\n");
            case (DC_DIMMER_STATUS_2):
                RV_PRINTF("LightDevice::executeCommand: !!!!!!!!!! CURRENTLY DO NOT Handle DC_DIMMER_STATUS_1 or 2 !!!!!!!!!!!!\n");
            case (DC_DIMMER_STATUS_3):
                // then we don't send a command on the CAN bus, we update our views (HOME SPAN)
                // the -> the views will requst the data from the buffer 
                // RV_PRINTF("LightDevice::executeCommand: Handling DC_DIMMER_STATUS_3\n");
                if (rawData != nullptr) {
                    setData(dgn, rawData); // set the current data to the new data
                    updateViews(); // update the views with the new data
                    cmdExecuted = true;
                } else {
                    RV_PRINTF("LightDevice::executeCommand: No data received for DC_DIMMER_STATUS_3\n");
                }
                break;

            default:
                RV_PRINTF("LightDevice::executeCommand: Unknown DGN %d received, cannot execute command.\n", dgn);
                break;
        }
    }
    return cmdExecuted; // Command execution failed
}
