wahart77399/RV-Bridge/src/Devices/Controllable/Switches/LightDeviceView.cpp

#include "RVConstants.h"
/*********************************************************************************
 *  MIT License
 *  
 *  Copyright (c) 2023 Randy Ubillos
 *  
 *  https://github.com/rubillos/RV-Bridge
 *  
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
 ********************************************************************************/
 
////////////////////////////////////////////////////////////////
//                                                            //
//    RV-Bridge: A HomeKit to RV-C interface for the ESP32    //
//                                                            //
////////////////////////////////////////////////////////////////

#include "LightDeviceView.h"
#include "LightDevice.h"
#include "Packet.h"
#include "PacketQueue.h"
#include "debug.h"


bool LightDeviceView::bridgeCreated = false;
boolean LightDeviceView::isItDimmable(void)  {
    boolean result = false;
    LightDevice* mdl = static_cast<LightDevice* >(this->getModel());
    if (mdl != nullptr) {
        result = mdl->isDimmable();
    }
    return result;
}

void LightDeviceView::setItOn(bool on) { 
    LightDevice* mdl = static_cast<LightDevice*>(this->getModel());
    if (mdl != nullptr)
        mdl->setOn(on);
}

void LightDeviceView::setItsBrightness(uint8_t val) {
    LightDevice* mdl = static_cast<LightDevice*>(this->getModel());
    if (mdl != nullptr)
        mdl->setBrightnessRaw(val);
}

LightDeviceView::LightController::LightController(LightDeviceView* vw, GenericDevice* mdl, const char* spanDeviceName)
        : Service::LightBulb(),
            power(nullptr),
            brightness(nullptr),
            model(nullptr),
            view(nullptr) {
    power = new Characteristic::On();
    this->model = static_cast<LightDevice* >(mdl);
    view = vw;
    if ((vw != nullptr) && vw->isItDimmable()) 
        brightness = new Characteristic::Brightness(DIMMER_QUARTER_BRIGHTNESS); // start with 1/4
}

bool LightDeviceView::LightController::update(void) {                              // update() method
        boolean result = false;
        view->dontUpdateTheView(); 
        if (model != nullptr && view != nullptr && power != nullptr) {
            uint8_t* rawData = model->getCurrentData();
            bool powerChanged = power->updated();
            bool brightnessChanged = brightness != nullptr && brightness->updated() && view->isItDimmable();

            if (powerChanged && !isOn()) {
                view->setItOn(false);
            } else if (brightnessChanged) {
                uint8_t pct = brightness->getNewVal();
                view->setItsBrightness(pct);
            } else if (powerChanged) {
                view->setItOn(true);
            }
            RV_PRINTF("LightDeviceView::LightDeviceController::update - on: %d\n", model->isOn());
            model->executeCommand(DC_DIMMER_COMMAND, rawData);
            result = true;
        }
        view->updateTheView();
        return(result);                               // return true
} // update

void LightDeviceView::createBridge(void) {
    if (!LightDeviceView::bridgeCreated) {
        RV_PRINTF("LightDeviceView::createBridge called\n");
        // create the bridge for the light switch
        // homeSpan.begin(Category::Bridges, "RV-Bridge-On-Off-Switch", DEFAULT_HOST_NAME, "RV-Bridge-ESP32");
        // new SpanAccessory(); 
        // new Service::AccessoryInformation();
        // new Characteristic::Identify();
        LightDeviceView::bridgeCreated = true;
        // RV_PRINTF("LightDeviceView::createBridge completed\n");
    }
}



#include "ChassisMobility.h"
bool LightDeviceView::updateView(void) {
    // the light switch may have been turned on/off at the wall and thus needs to be reflected in the SpanView
    // 
    // RV_PRINTF("LightDeviceView::updateView called\n");
    bool updated = false;
    if (isNeedToUpdateView() && ChassisMobility::isParked()) { // don't mess with the state of the lock when the change is is initiated by the controller and not the model
        uint8_t instance = indexOfModel();   
        uint8_t index = -1;
        LightDevice* mdl = static_cast<LightDevice*>(getModel());
        if (mdl != nullptr) {
            // RV_PRINTF("DC_SwitchView::updateView - mdl not null\n");
            index = mdl->index();;
            // toggle the switch state
            boolean on = mdl->isOn();
            // RV_PRINTF("DC_SwitchView::updateView - on=%d\n", on);
            controller.turnOn(on);
            if (mdl->isDimmable())
                controller.setBrightness(mdl->getBrightness());
            if (index == 0)
                // RV_PRINTF("LightDeviceView::updateView - power = %d, controller.isOn() = %d\n", on, controller.isOn());
                // mdl->setLockedFlag(!locked);
                ;
            updated = true;
        }        
        // RV_PRINTF("LightDeviceView::updateView completed \n"); 
    }
    return updated;
}


// const char* LightDeviceView::name = "LightBulb"; // from Span.h
// const char* LightDeviceView::type = "43"; // from Span.h

LightDeviceView::LightDeviceView(GenericDevice* model, const char* spanDevName) : SpanView(model), controller(this, model, spanDevName) {

}

void LightDeviceView::createLightDeviceView(GenericDevice* model, const char* spanDevName) {
    RV_PRINTF("LightDevice::createLightDevice called\n");
    SpanView::prepHomeSpan();

    SpanView::createAccessory();
    new Service::AccessoryInformation(); 
    new Characteristic::Identify();
    new Characteristic::Name(spanDevName);
    LightDeviceView* tmp = new LightDeviceView(model, spanDevName);
    if (tmp != nullptr)
        RV_PRINTF("LightDeviceView::createLightDeviceView: tmp created successfully\n");
    else
        RV_PRINTF("LightDeviceView::createLightDeviceView: tmp creation failed\n");   
    RV_PRINTF("LightDeviceView::createLightDeviceView completed\n");
}
