wahart77399/RV-Bridge/src/Devices/Sensors/Power/AutomaticTransferSwitch.h

#ifndef AUTOMATIC_TRANSFER_SWITCH_H
#define AUTOMATIC_TRANSFER_SWITCH_H // once I'm ready to define this, move this below ifndef

/*********************************************************************************
 *  MIT License
 *  
 *  Copyright (c) 2023 Randy Ubillos
 *  
 *  https://github.com/rubillos/RV-Bridge
 *  
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
 ********************************************************************************/
 
////////////////////////////////////////////////////////////////
//                                                            //
//    RV-Bridge: A HomeKit to RV-C interface for the ESP32    //
//                                                            //
////////////////////////////////////////////////////////////////
#include "RVConstants.h"
#include "debug.h"
#include "Arduino.h"
#include <cstring>
#include "PowerSensor.h"
#include "ATS_Definitions.h"

class AutomaticTransferSwitch : public PowerSensor {
    friend class DeviceFactory;
    public:
        static const uint8_t ATS_BYTE_0 = 0; 
        static const uint8_t ATS_STATUS_INDEX_MASK  = 0x07;  // 0000 0111
        static const uint8_t ATS_STATUS_IOTYPE_MASK = 0x08;  // 0000 1000
        static const uint8_t ATS_STATUS_SOURCE_MASK = 0x70;  // 0111 0000
        static const uint8_t ATS_STATUS_LEG_MASK    = 0x80;  // 1000 0000
    private:
        friend class AutomaticTransferSwitchView;
        char sourceNames_[7][33] = {
            "Primary", "Secondary", "Source 2", "Source 3", "Source 4", "Source 5", "Source 6"
        };
        char sourceStatusDetail_[65] = {};
        static constexpr uint8_t SOURCE_COUNT = 7;
        static constexpr uint8_t LEG_COUNT = 2;
        uint8_t selectedSource_ = 0xFF;
        uint8_t sourceReadings_[SOURCE_COUNT][LEG_COUNT][NUMIO][DATA_SIZE] = {};
        bool sourceReadingReceived_[SOURCE_COUNT][LEG_COUNT][NUMIO] = {};

        void setSourceName(uint8_t source, const char* name) {
            if (source < 7 && name != nullptr && name[0] != '\0') {
                std::strncpy(sourceNames_[source], name, sizeof(sourceNames_[source]) - 1);
                sourceNames_[source][sizeof(sourceNames_[source]) - 1] = '\0';
            }
        }

        static uint8_t byte0(const uint8_t* raw) {
            uint8_t result = 0;
            if (raw != nullptr) {
                result = raw[ATS_BYTE_0];
            }
            return result;
        }

        uint8_t getInstance(void) const {
            uint8_t* rawData = getCurrentData();
            uint8_t result = ATS_INSTANCE_0_INVALID; // default to invalid
            if (rawData != nullptr) {
                result = static_cast<uint8_t> (byte0(rawData) & ATS_INSTANCE_MASK);// rawData[ATS_BYTE_0] & ATS_STATUS_INDEX_MASK; // get the instance index
            }
            return result;
        }

        bool isInstanceValid(void) const {
            uint8_t instance = getInstance();
            return (instance > ATS_INSTANCE_0_INVALID) && (instance < ATS_INSTANCE_7_INVALID);
        }

        ATS_IO_TYPE getIOType(void) const {
            uint8_t* rawData = getCurrentData();
            ATS_IO_TYPE result = ATS_IO_Type::Input; // default to input
            if (rawData != nullptr) {
                result = static_cast<ATS_IO_TYPE> ((byte0(rawData) & ATS_IOTYPE_MASK) >> ATS_IOTYPE_SHIFT); // get the IO type
            }
            return result;
        }

        ATS_SOURCE_TYPE getSource(void) const {
            uint8_t* rawData = getCurrentData();
            ATS_SOURCE_TYPE result = ATSSource::NoData; // default to primary source 
            if (rawData != nullptr) {
                result = static_cast<ATS_SOURCE_TYPE> ((byte0(rawData) & ATS_SOURCE_MASK) >> ATS_SOURCE_SHIFT); // get the source type
            }
            return result;
        }   

        ATS_LEG_TYPE getLeg(void) const {
            uint8_t* rawData = getCurrentData();
            ATS_LEG_TYPE result = ATSLeg::Leg1; // default to leg 1
            if (rawData != nullptr) {
                result = static_cast<ATS_LEG_TYPE> ((byte0(rawData) & ATS_LEG_MASK) >> ATS_LEG_SHIFT); // get the leg type
            }
            return result;
        }

    protected:
        void setData(RVC_DGN dgn, uint8_t* data) override;
        uint8_t lineOf(RVC_DGN /*dgn*/, const uint8_t* raw) const override {
            return static_cast<uint8_t>((byte0(raw) & ATS_LEG_MASK) >> ATS_LEG_SHIFT);
        }

        uint8_t ioOf(RVC_DGN /*dgn*/, const uint8_t* raw) const override {
            const uint8_t ioType = static_cast<uint8_t>((byte0(raw) & ATS_IOTYPE_MASK) >> ATS_IOTYPE_SHIFT);
            return (ioType == static_cast<uint8_t>(ATS_IO_Type::Output)) ? OUTPUT_LINE : INPUT_LINE;
        }
        
        // virtual CAN_frame_t* buildCommand(RVC_DGN dgn); // do nothing - no commands will be sent to the ATS - we listen only

    public:

        
        void attachView(const char* name, bool showCurrent = true, bool showFault = true) override;

        AutomaticTransferSwitch(uint8_t address, uint8_t index) : PowerSensor(address, index) { 
        }

        virtual ~AutomaticTransferSwitch() {
            // Destructor implementation
        } 

        virtual boolean executeCommand(RVC_DGN dgn, const uint8_t* buffer, uint8_t val=SOURCE_ADDRESS); // this is only to deal with ATS dgns
};

#endif // AUTOMATIC_TRANSFER_SWITCH_H // HOW_KIT_2
