wahart77399/RV-Bridge/src/Devices/Sensors/Tanks.h

#include "RVConstants.h"
#ifndef TANKS_H
#define TANKS_H // once I'm ready to define this, move this below ifndef


#include "Arduino.h"
#include "GenericDevice.h"
#include "TanksDefinition.h"
#include <map>
#include "debug.h"



// TANKS is only (for now) a sensor, not a controller where we can start/stop it
// Initially, we are only going to monitor line output of TANKS, but we may add status of the TANKS in general at a later point
class Tanks : public GenericDevice {
    public: 

        static const uint8_t TANKS_INDEX; //                  = 0; 
        static const uint8_t TANKS_RELATIVE_LEVEL; //         = 1;  
        static const uint8_t TANKS_RESOLUTION; //             = 2;  
        static const uint8_t TANKS_ABSOLUTE_LEVEL_MSB; //     = 3;
        static const uint8_t TANKS_ABSOLUTE_LEVEL_LSB; //     = 4;
        static const uint8_t TANKS_SIZE_MSB; //               = 5;
        static const uint8_t TANKS_SIZE_LSB; //               = 6; 
        static const uint8_t FRESH_WATER_INSTANCE; //         = 0;
        static const uint8_t BLACK_WATER_INSTANCE; //         = 1;
        static const uint8_t GRAY_WATER_INSTANCE; //          = 2;
        static const uint8_t LPG_INSTANCE; //                 = 3;
        static const uint8_t FRESH_WATER_SECOND_INSTANCE; //  = 16;
        static const uint8_t BLACK_WATER_SECOND_INSTANCE; //  = 17;
        static const uint8_t GRAY_WATER_SECOND_INSTANCE; //   = 18;
        static const uint8_t LPG_SECOND_INSTANCE; //          = 19;
        static const std::map<uint8_t, std::string> tankNames; // = { {FRESH_WATER_INSTANCE, "Fresh Water"}, {BLACK_WATER_INSTANCE, "Black Water"}, {GRAY_WATER_INSTANCE, "Gray Water"}, {LPG_INSTANCE, "LPG"} }    ;

    private:
        friend class TanksView;
        uint16_t tankSize; // in liters
        uint8_t autoFillStatusData_ = 0xFF;
        bool autoFillStatusReceived_ = false;

        void setAutoFillStatus(const uint8_t* data);
        bool hasAutoFillOperatingStatus() const;
        bool autoFillOperating() const;
        bool hasAutoFillValveStatus() const;
        bool autoFillValveOpen() const;
        bool hasAutoFillResult() const;
        bool autoFillResultFailed() const;
        uint8_t levelPercent() const;

        uint16_t size(void) const { 
            uint16_t result = tankSize;
            uint8_t* rawData = getCurrentData();
            if (rawData != nullptr) {
                uint16_t reportedSize = getLilEndian(rawData[TANKS_SIZE_MSB], rawData[TANKS_SIZE_LSB]);
                if (reportedSize > 0 && reportedSize <= MAX_RVC_TANK_VALUE) {
                    result = reportedSize;
                }
            }
            return result;
        }

        uint16_t level(void) const {
            uint16_t result = INVALID_TANK_SIZE;
            uint8_t* rawData = getCurrentData();
            if (rawData != nullptr) {
                uint16_t tankLevel = getLilEndian(rawData[TANKS_ABSOLUTE_LEVEL_MSB], rawData[TANKS_ABSOLUTE_LEVEL_LSB]);
                if (tankLevel <= MAX_RVC_TANK_VALUE)
                    result = tankLevel;
                }
            return result;
        }


    protected:
        
        // virtual CAN_frame_t* buildCommand(RVC_DGN dgn); // do nothing - no commands will be sent to the TANKS - we listen only
        virtual void setData(RVC_DGN dgn, uint8_t* sourceData) {
                    uint8_t* destinationData = getCurrentData();
                    if ((sourceData != nullptr) && (destinationData != nullptr)) {
                        for (int i = 0; i < 8; i++) {
                            destinationData[i] = sourceData[i];
                        }
                    }
                }
        
        virtual CAN_frame_t* buildCommand(RVC_DGN dgn); // do nothing - no commands will be sent to the TANKS - we listen only


    public:

        Tanks() : GenericDevice(), tankSize(INVALID_TANK_SIZE) {
            // Constructor implementation
        }

        Tanks(const Tanks&) = delete;
        Tanks& operator=(const Tanks&) = delete;

        Tanks(uint8_t address, uint8_t index, uint16_t size) : GenericDevice(address, index), tankSize(size) { 
        }

        Tanks(uint8_t* data) : GenericDevice(data), tankSize(INVALID_TANK_SIZE) {
            // Constructor with parameters implementation
        }

        Tanks(Tanks&&) = delete;
        Tanks& operator=(Tanks&&) = delete;

        virtual ~Tanks() {
            // Destructor implementation
        } 

        virtual boolean executeCommand(RVC_DGN dgn, const uint8_t* buffer, uint8_t val=SOURCE_ADDRESS); // this is only to deal with TANKS dgns

};


#endif // TANKS_H
